any-sliv/time_tracker_esp32/app/imu/mpu6050.hpp

/**
 * @file mpu6050.hpp
 * @author Maciej Sliwinski
 * @brief This file is a part of time_tracker_esp32 project.
 *
 * The code is distributed under the MIT License.
 * See the LICENCE file for more details.
 */

#pragma once

#include "i2c.hpp"

#define	SMPLRT_DIV		0x19	//陀螺仪采样率，典型值：0x07(125Hz)
#define	CONFIG			0x1A	//低通滤波频率，典型值：0x06(5Hz)
#define	GYRO_CONFIG		0x1B	//陀螺仪自检及测量范围，典型值：0x18(不自检，2000deg/s)
#define	ACCEL_CONFIG	0x1C	//加速计自检、测量范围及高通滤波频率，典型值：0x01(不自检，2G，5Hz)
#define	ACCEL_XOUT_H	0x3B	
#define	ACCEL_XOUT_L	0x3C
#define	ACCEL_YOUT_H	0x3D
#define	ACCEL_YOUT_L	0x3E
#define	ACCEL_ZOUT_H	0x3F
#define	ACCEL_ZOUT_L	0x40
#define	TEMP_OUT_H		0x41
#define	TEMP_OUT_L		0x42
#define	GYRO_XOUT_H		0x43
#define	GYRO_XOUT_L		0x44	
#define	GYRO_YOUT_H		0x45
#define	GYRO_YOUT_L		0x46
#define	GYRO_ZOUT_H		0x47
#define	GYRO_ZOUT_L		0x48
#define	PWR_MGMT_1		0x6B	//电源管理，典型值：0x00(正常启用)
#define	PWR_MGMT_2		0x6C
#define	WHO_AM_I		0x75	//IIC地址寄存器(默认数值0x68，只读)
#define	MPU6050_ADDR	0x68	//IIC写入时的地址字节数据，+1为读取

class MPU6050 {
private:
    I2C *i2c;

    void enableSleepCycling();
public:
    MPU6050() = delete;
    MPU6050(MPU6050& copy) = delete;
    MPU6050(gpio_num_t scl, gpio_num_t sda, i2c_port_t port);
    ~MPU6050();
    bool init();

    float getAccX();
    float getAccY();
    float getAccZ();

    float getGyroX();
    float getGyroY();
    float getGyroZ();

};
